solvek/Garden-Monitor/gmonitor/ConfigSample.h

// How long to show time on display (seconds)
#define DELAY_TIME 12
// How long to show date on display (seconds)
#define DELAY_DATE 4
// How long to show temperature on display (seconds)
#define DELAY_TEMP 4
